transistorfet/retroverse/images/basic-single-cpu-system-angle.jpg

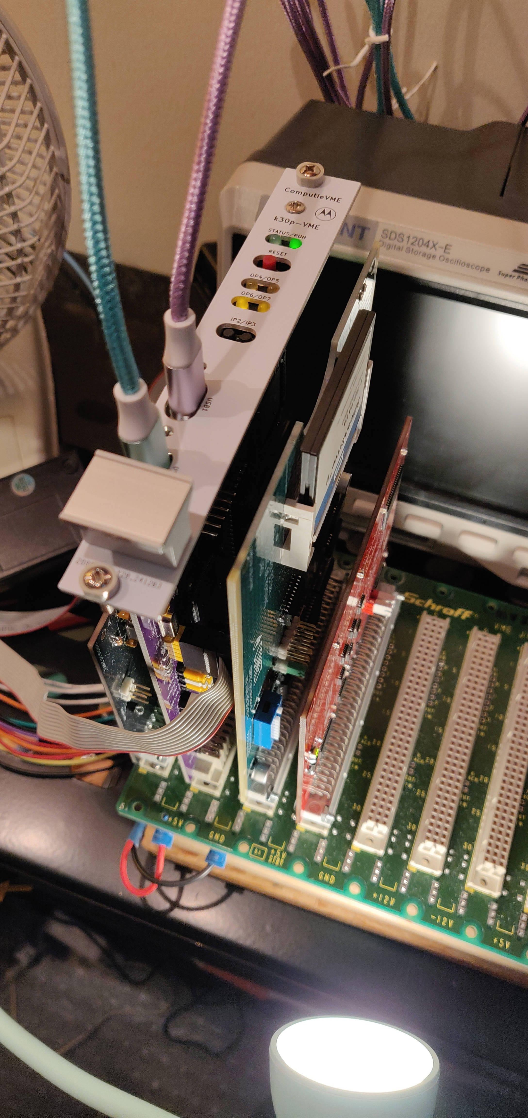
images/basic-single-cpu-system-angle.jpg
