transistorfet/retroverse/images/basic-single-cpu-system-top-angle.jpg

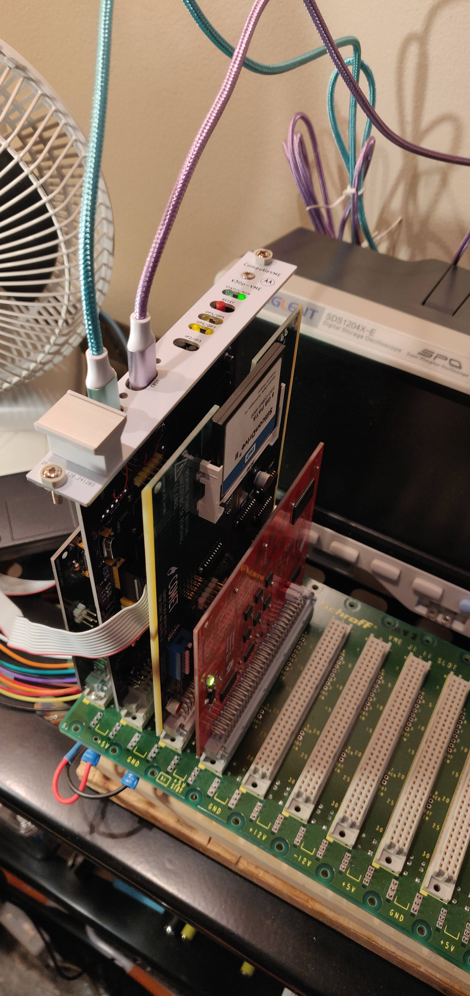
images/basic-single-cpu-system-top-angle.jpg
