transistorfet/retroverse/images/basic-single-cpu-system-top.jpg

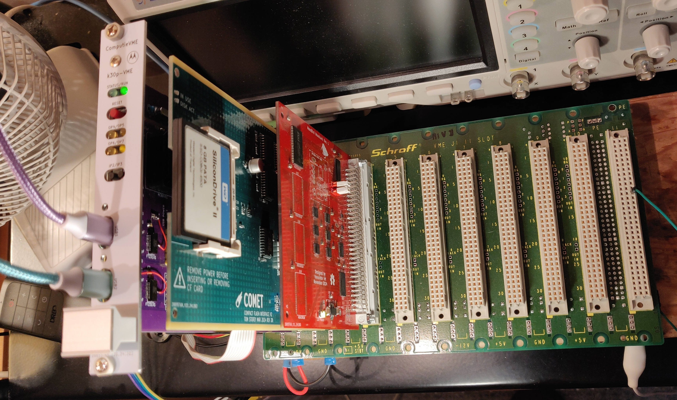
images/basic-single-cpu-system-top.jpg
