transistorfet/retroverse/images/BigBoy-rev.1-frontpanel.jpg

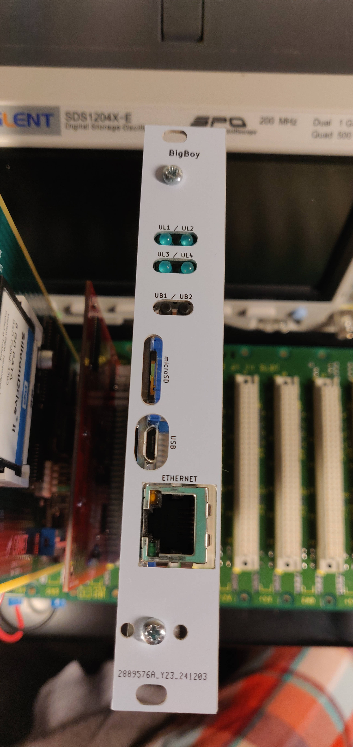
images/BigBoy-rev.1-frontpanel.jpg
