transistorfet/retroverse/images/BigBoy-rev.1.jpg

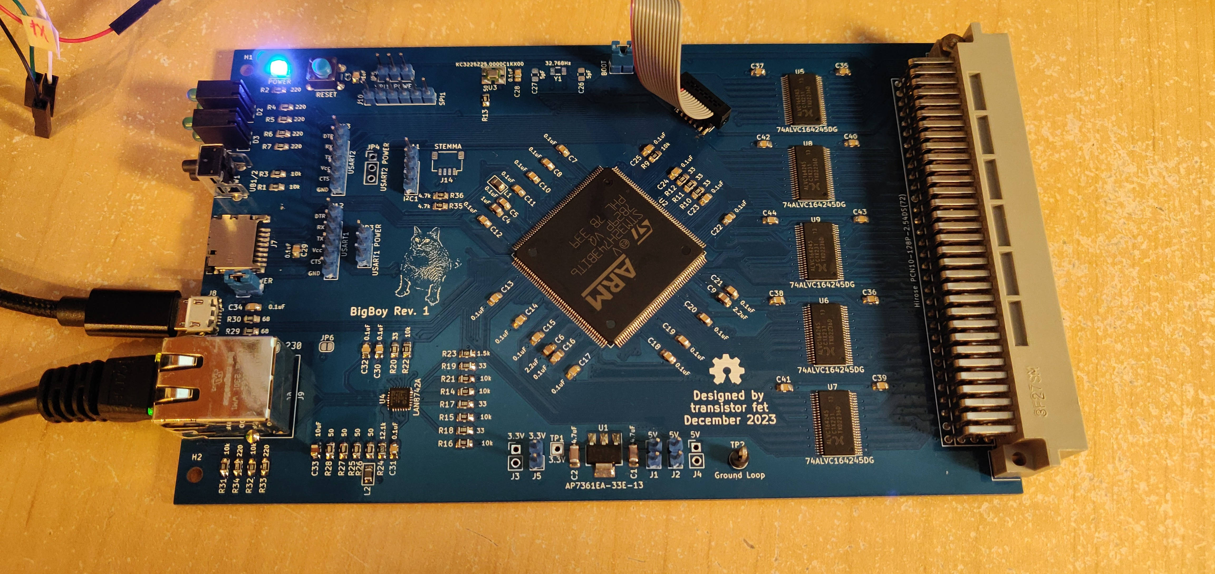
images/BigBoy-rev.1.jpg
