transistorfet/retroverse/images/COMET-CFInterface-rev.2b.jpg

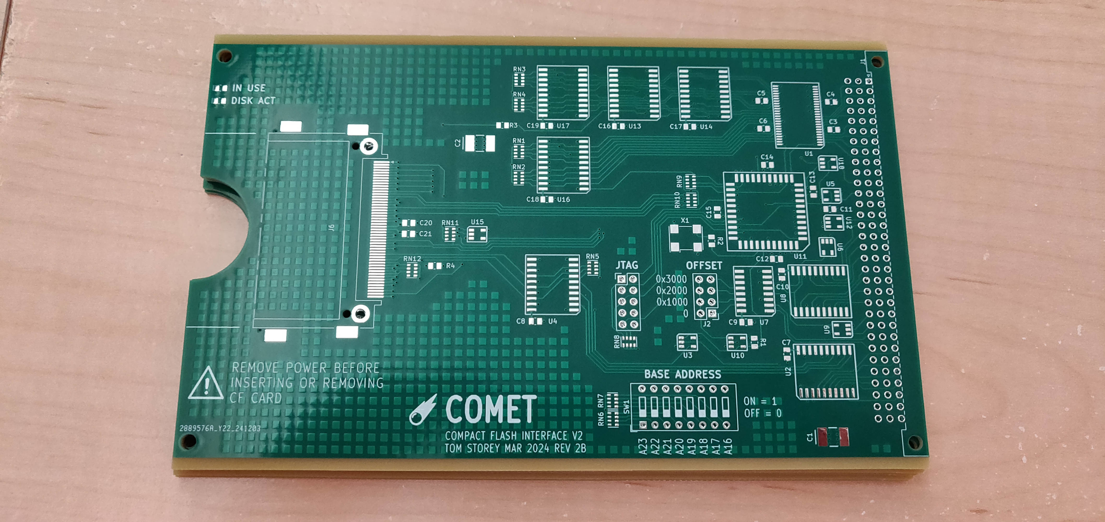
images/COMET-CFInterface-rev.2b.jpg
