transistorfet/retroverse/images/complete-single-cpu-system-angle.jpg

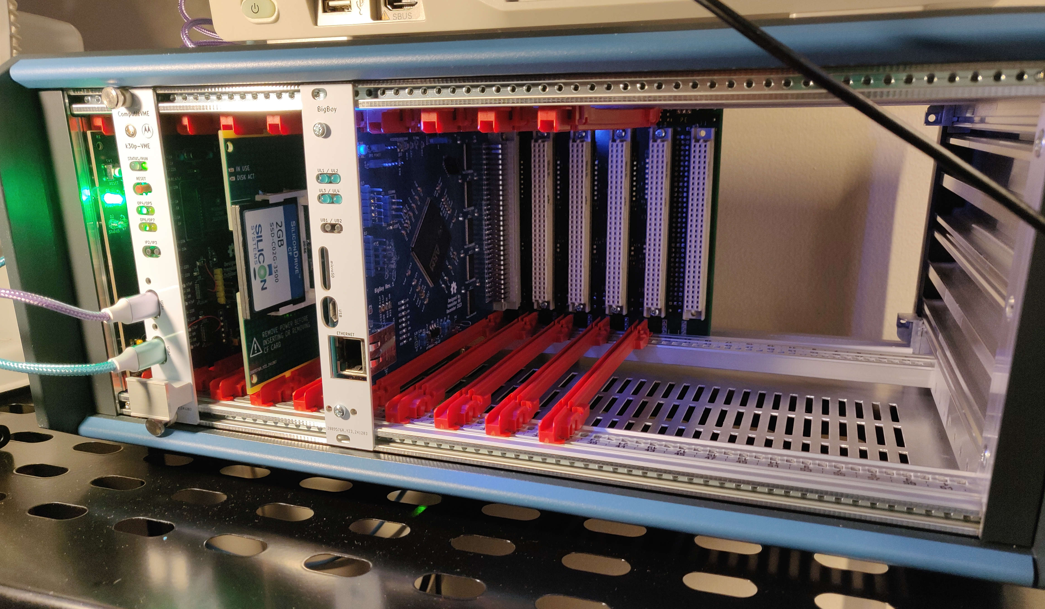
images/complete-single-cpu-system-angle.jpg
