transistorfet/retroverse/images/complete-single-cpu-system-closeup.jpg

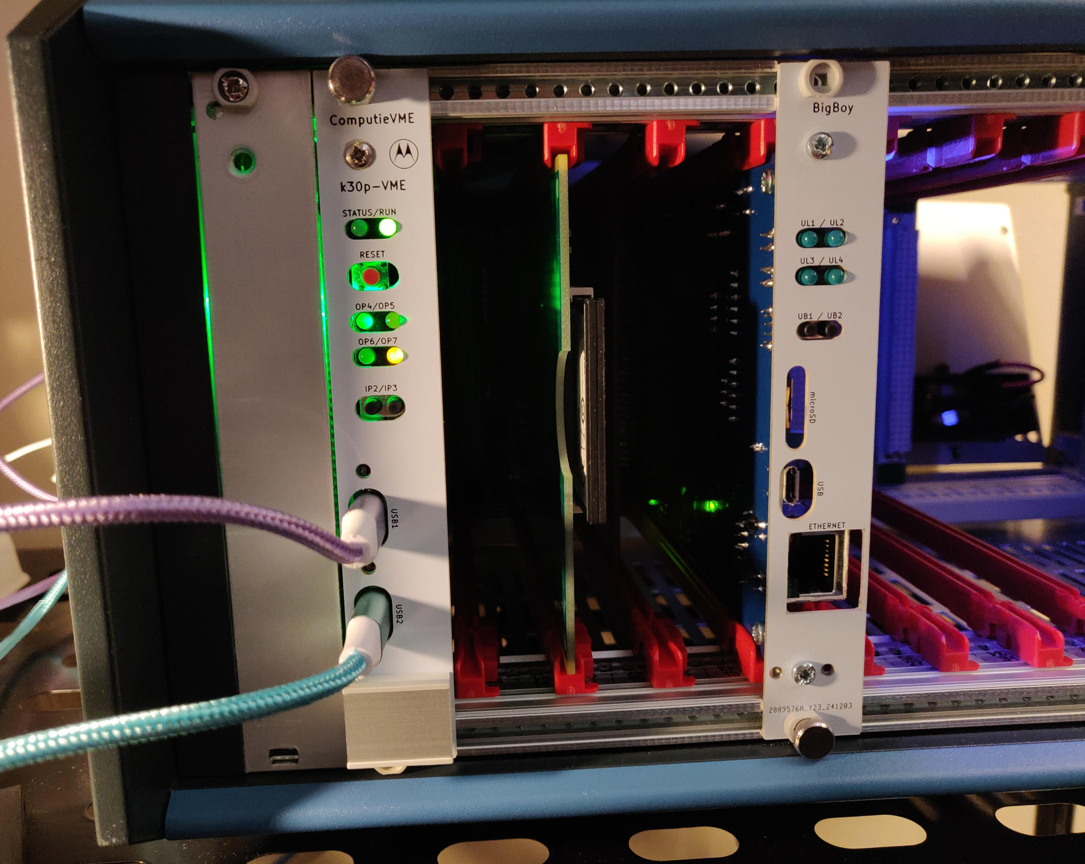
images/complete-single-cpu-system-closeup.jpg
