transistorfet/retroverse/images/complete-single-cpu-system-computie-closeup.jpg

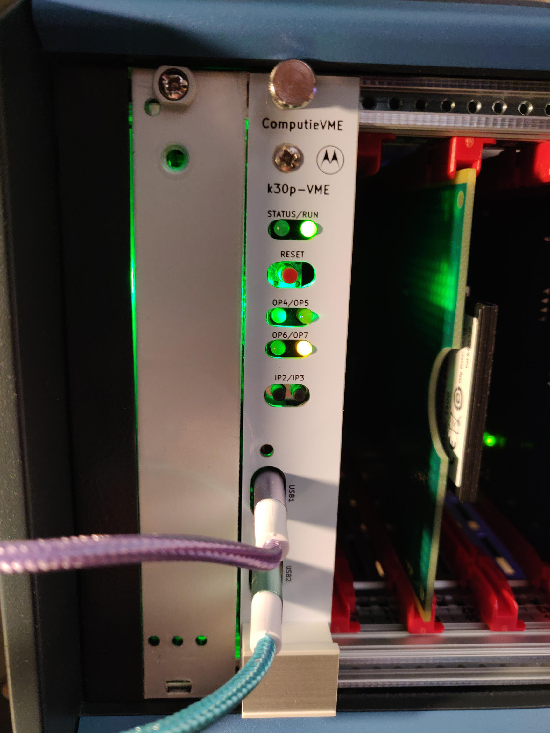
images/complete-single-cpu-system-computie-closeup.jpg
