transistorfet/retroverse/images/complete-single-cpu-system-front2.jpg

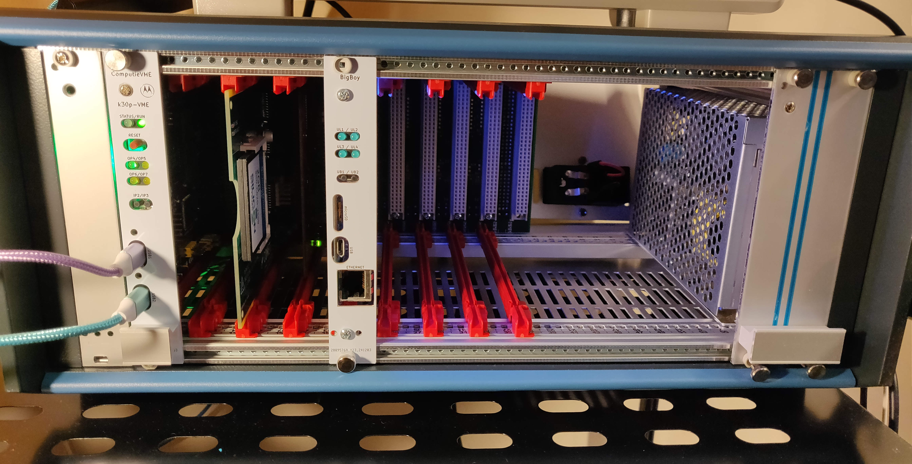
images/complete-single-cpu-system-front2.jpg
