transistorfet/retroverse/images/complete-single-cpu-system-front.jpg

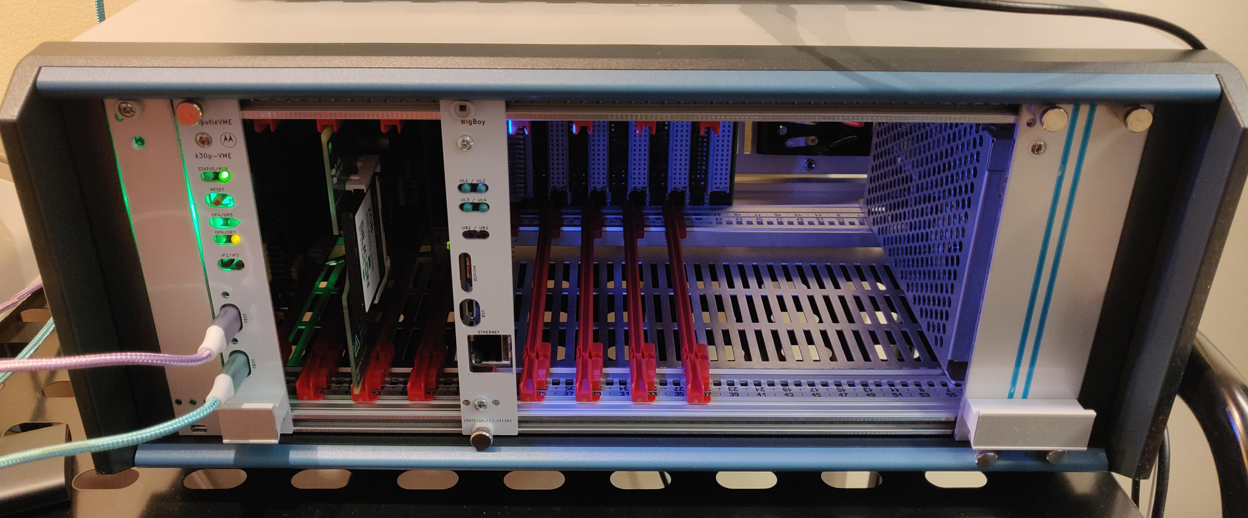
images/complete-single-cpu-system-front.jpg
