transistorfet/retroverse/images/k30p-rev.1-frontpanel.jpg

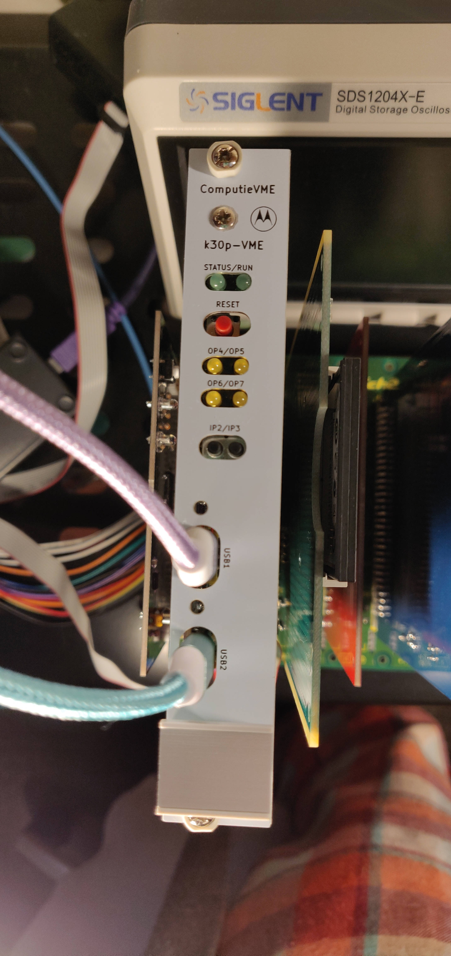
images/k30p-rev.1-frontpanel.jpg
