transistorfet/retroverse/images/k30p-VME-rev.1-frontpanel.jpg

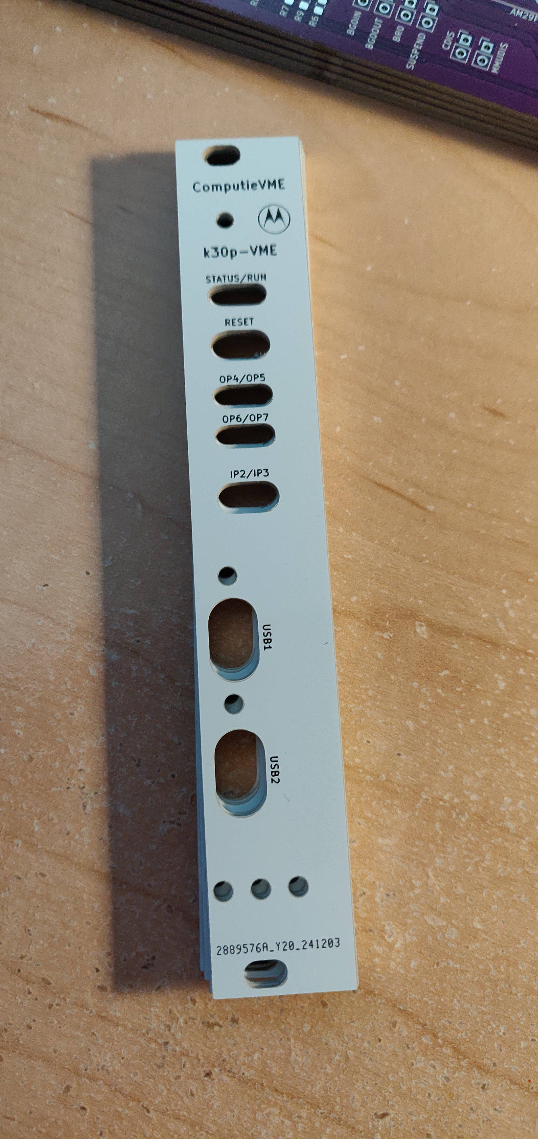
images/k30p-VME-rev.1-frontpanel.jpg
