transistorfet/retroverse/images/k30p-VME-rev.1-PCB.jpg

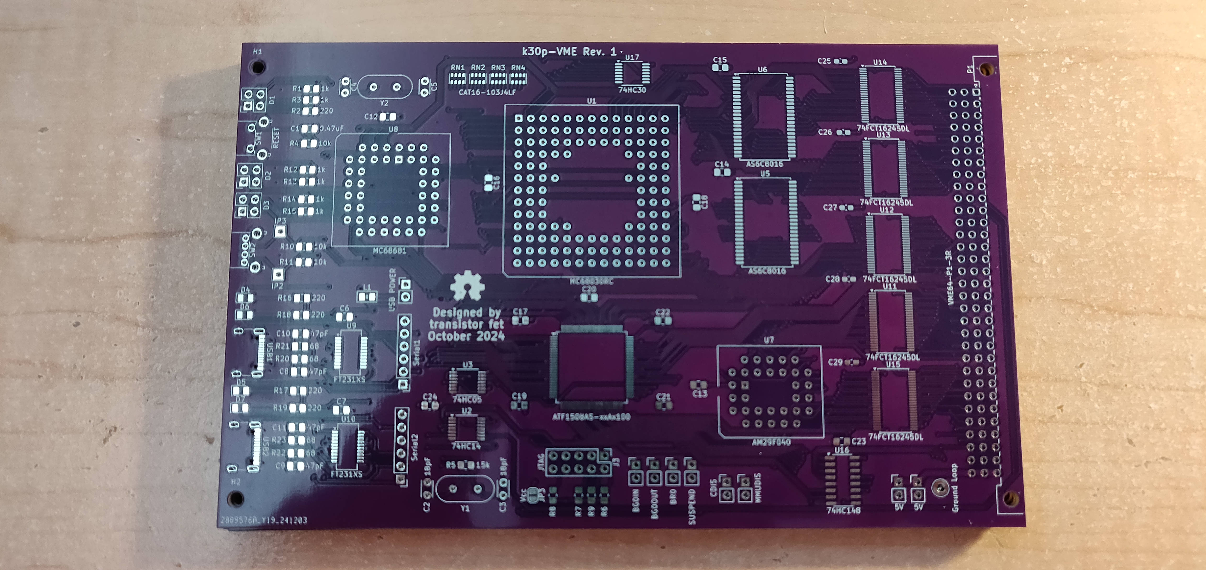
images/k30p-VME-rev.1-PCB.jpg
