transistorfet/retroverse/images/MembirdWoodcock-rev.1-PCB-backside.jpg

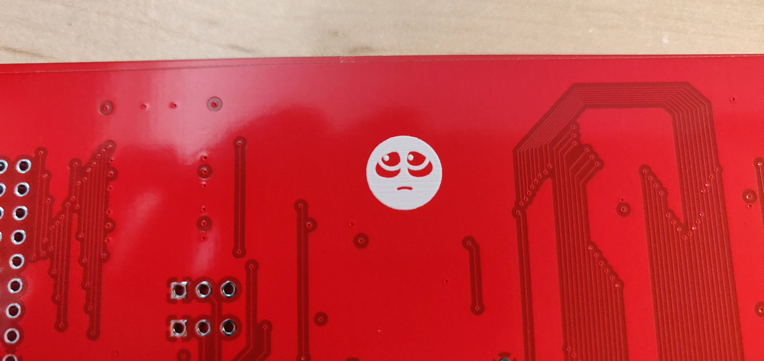
images/MembirdWoodcock-rev.1-PCB-backside.jpg
