transistorfet/retroverse/images/MembirdWoodcock-rev.1-PCB.jpg

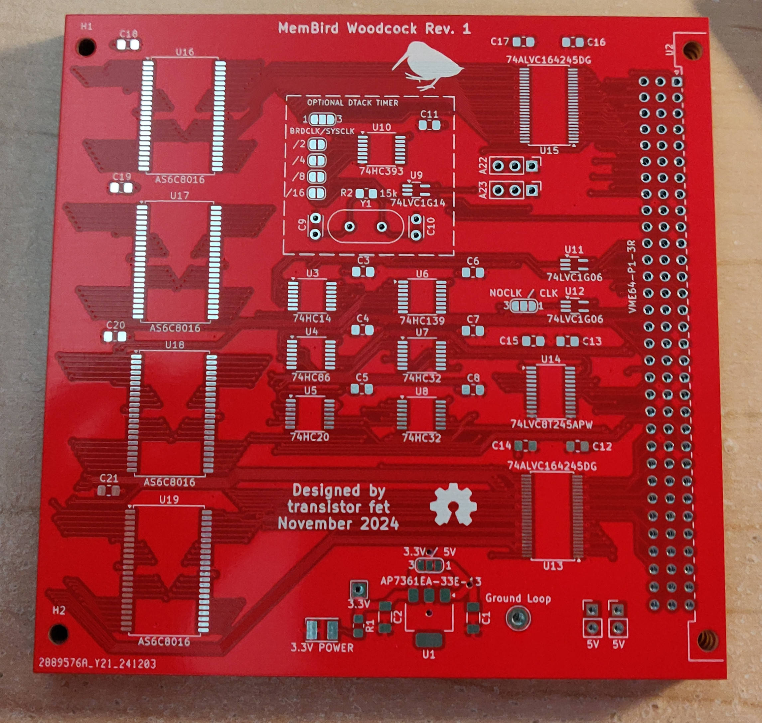
images/MembirdWoodcock-rev.1-PCB.jpg
