transistorfet/retroverse/images/Schroff-backplane-back.jpg

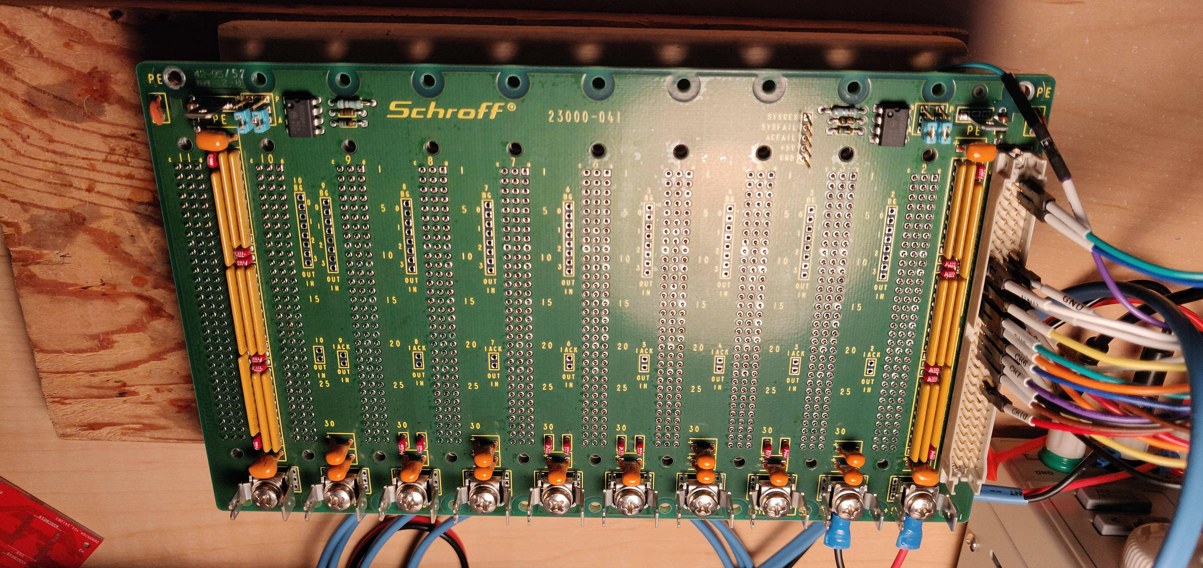
images/Schroff-backplane-back.jpg
