transistorfet/retroverse/images/Schroff-case-and-backplane-rear.jpg

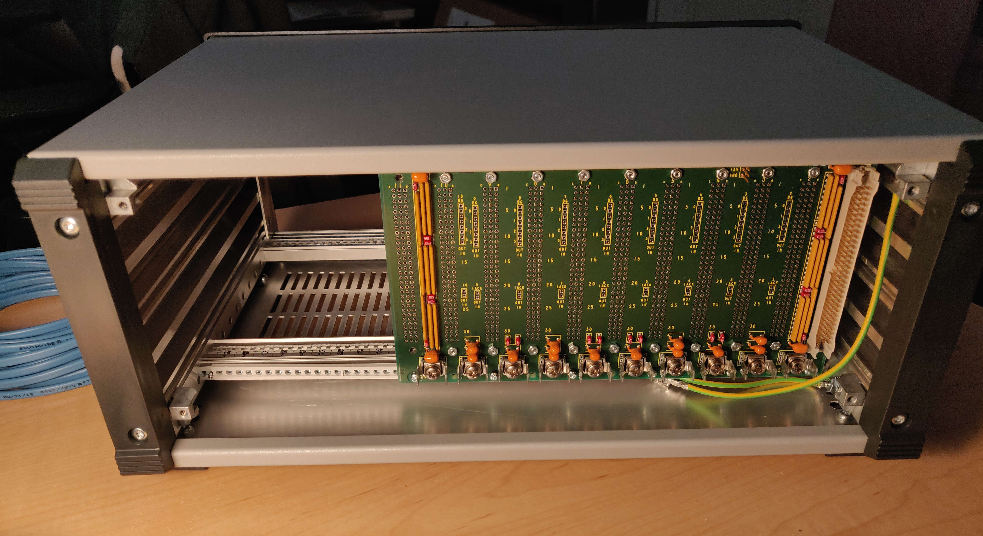
images/Schroff-case-and-backplane-rear.jpg
