transistorfet/retroverse/images/Schroff-case-and-backplane.jpg

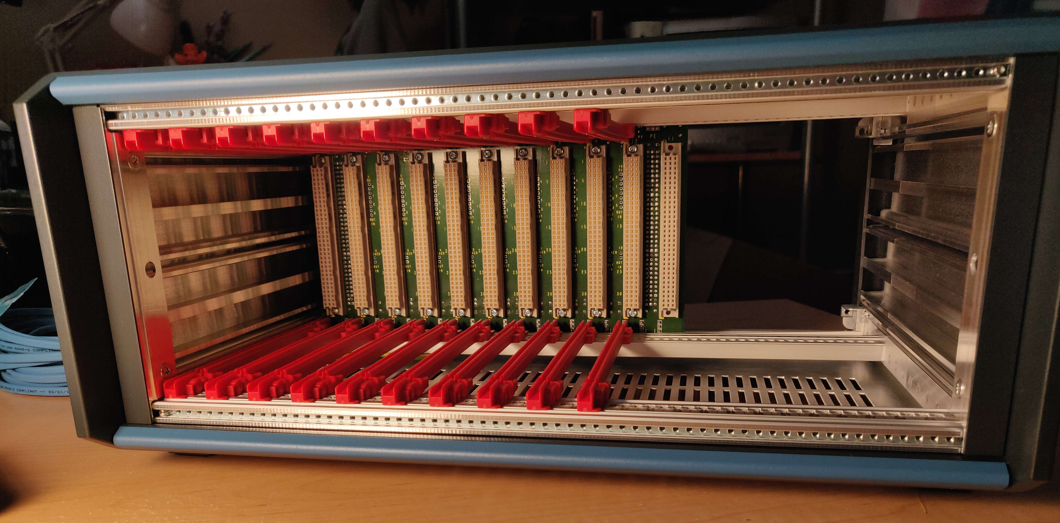
images/Schroff-case-and-backplane.jpg
