transistorfet/retroverse/images/Schroff-case-rear-panel-with-custom-switch.jpg

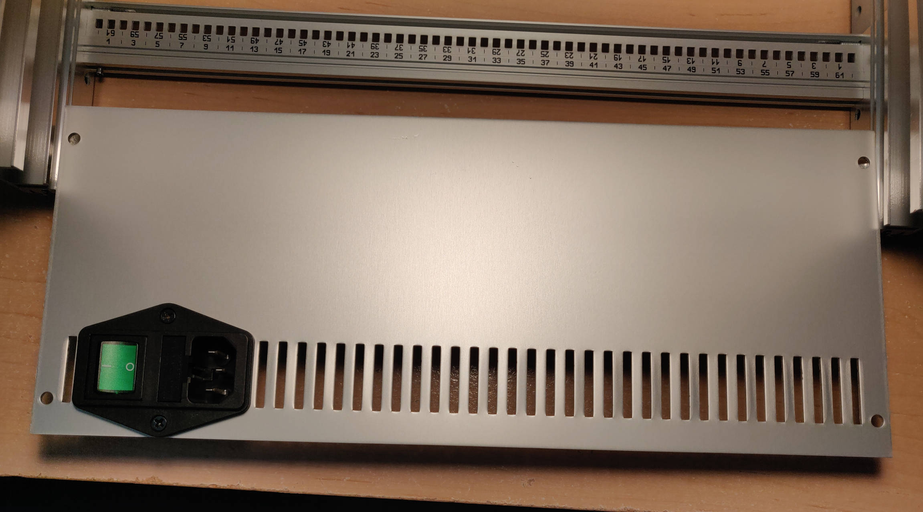
images/Schroff-case-rear-panel-with-custom-switch.jpg
