transistorfet/retroverse/images/Schroff-case-with-rear-panel-backside.jpg

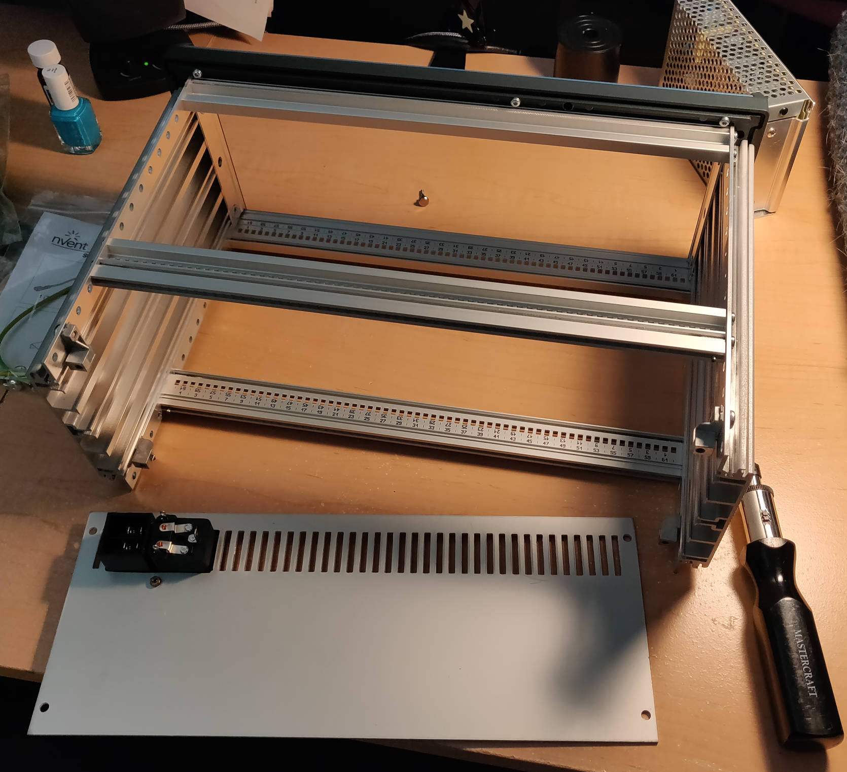
images/Schroff-case-with-rear-panel-backside.jpg
