transistorfet/retroverse/images/System-k30p-backplane.jpg

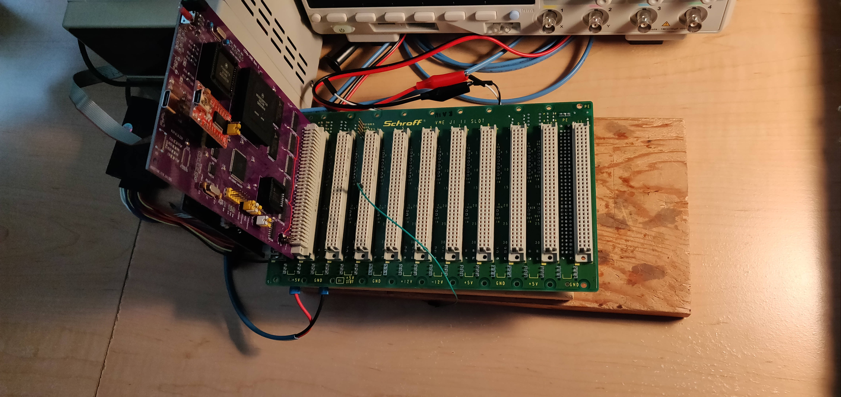
images/System-k30p-backplane.jpg
