transistorfet/retroverse/images/System-k30p-Membird-backplane-side.jpg

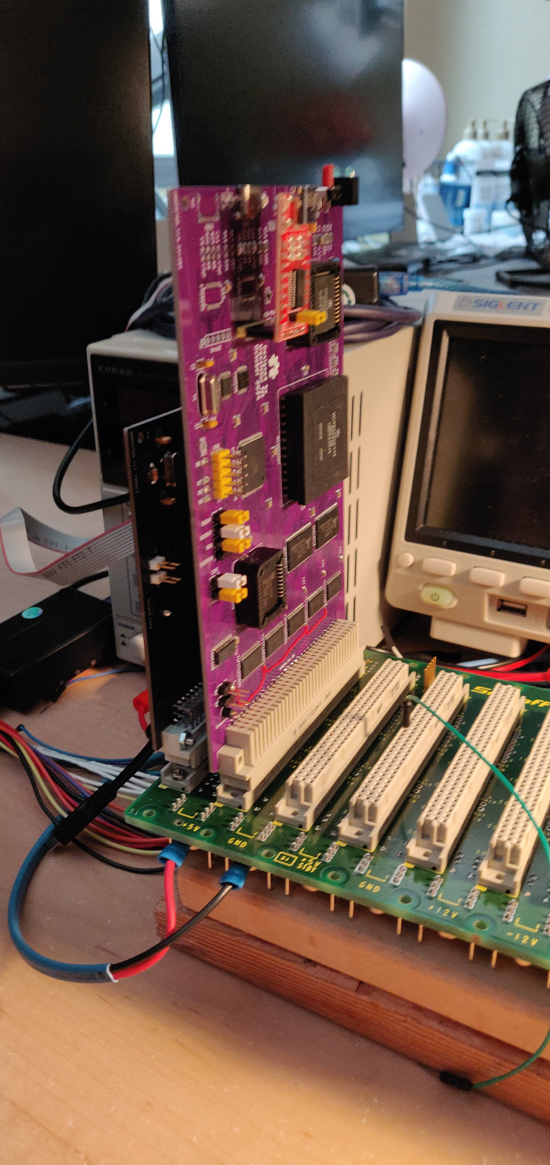
images/System-k30p-Membird-backplane-side.jpg
