transistorfet/retroverse/images/System-k30p-Membird-backplane-top.jpg

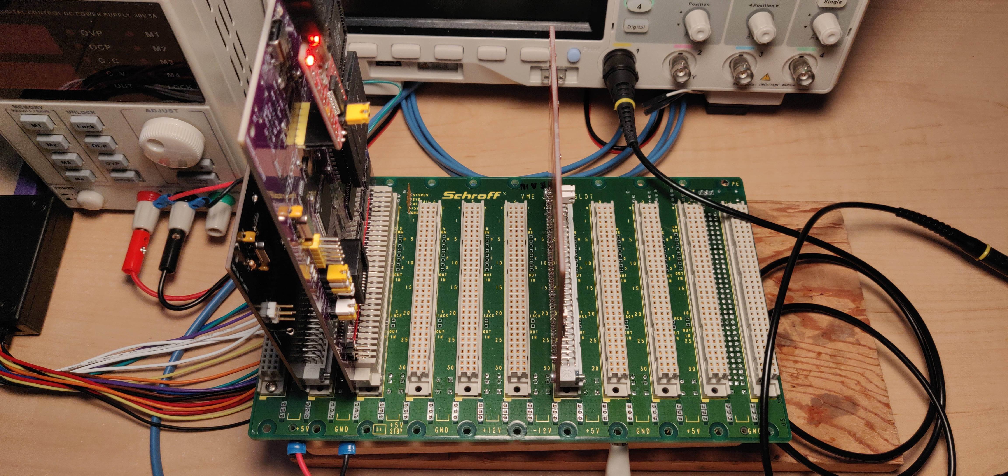
images/System-k30p-Membird-backplane-top.jpg
