transistorfet/retroverse/images/BigBoy-rev.1-assembled.jpg

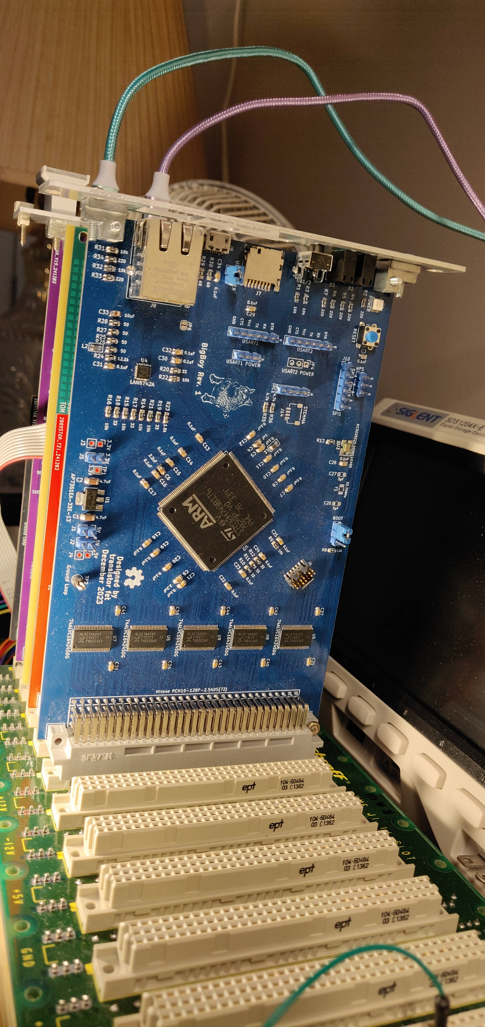
images/BigBoy-rev.1-assembled.jpg
