transistorfet/retroverse/images/k30p-VME-rev.1-reworked-assembled.jpg

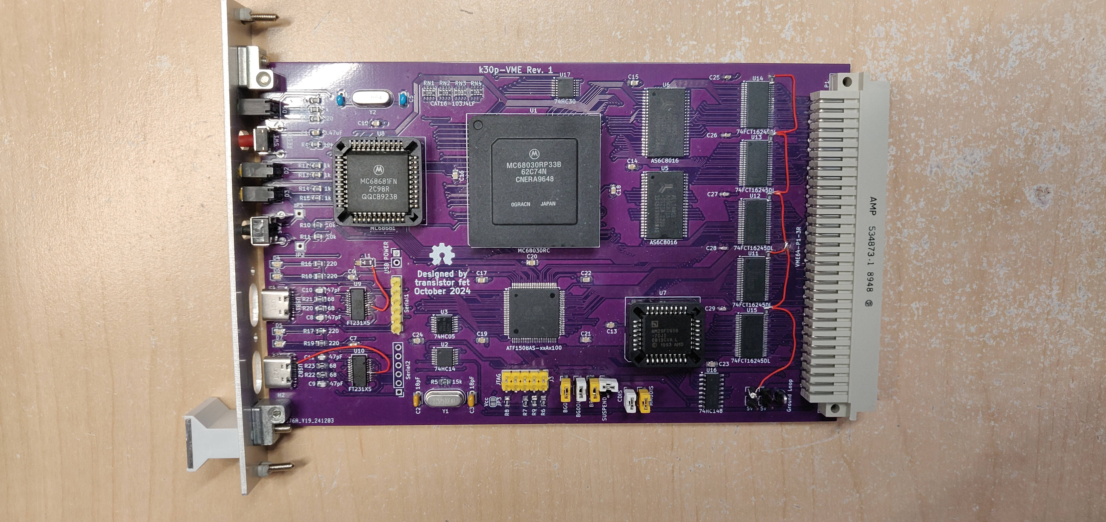
images/k30p-VME-rev.1-reworked-assembled.jpg
